asciilifeform/P4-HMD/fpga/async-fifo.v

// This file is part of the SPI controller for the Private Eye P4 HMD.
// Originally cribbed from WWW, but can't presently find where.

`default_nettype none

// Asynchronous FIFO module
module async_fifo #(

    // Parameters
    parameter DATA_SIZE = 8,  // Number of data bits
              ADDR_SIZE = 4,   // Number of bits for address
              MIN_FREE = 0 // Minimal free space for r_avail
) (

    // Inputs
    input [DATA_SIZE-1:0]      w_data,  // Data to be written to FIFO
    input                      w_en,    // Write data and increment addr.
    input                      w_clk,   // Write domain clock
    input                      w_rst,   // Write domain reset
    input                      r_en,    // Read data and increment addr.
    input                      r_clk,   // Read domain clock
    input                      r_rst,   // Read domain reset

    // Outputs
    output                     w_full,  // Flag: 1 if FIFO is full
    output reg [DATA_SIZE-1:0] r_data,  // Data to be read from FIFO
    output                     r_empty, // Flag: 1 if FIFO is empty
    output wire                avail    // 1 if FIFO has > MIN_FREE space
);

  // Constants
  localparam FIFO_DEPTH = (1 << ADDR_SIZE);

  // Internal signals
  wire [ADDR_SIZE-1:0] w_addr;
  wire [  ADDR_SIZE:0] w_gray;
  wire [ADDR_SIZE-1:0] r_addr;
  wire [  ADDR_SIZE:0] r_gray;

  // Internal storage elements
  reg  [  ADDR_SIZE:0] w_syn_r_gray;
  reg  [  ADDR_SIZE:0] w_syn_r_gray_pipe;
  reg  [  ADDR_SIZE:0] r_syn_w_gray;
  reg  [  ADDR_SIZE:0] r_syn_w_gray_pipe;

  // Declare memory
  reg  [DATA_SIZE-1:0] mem               [0:FIFO_DEPTH-1];

  //--------------------------------------------------------------------------
  // Dual-port memory (should be inferred as block RAM)

  // Write data logic for dual-port memory (separate write clock)
  // Do not write if FIFO is full!
  always @(posedge w_clk) begin
    if (w_en & ~w_full) begin
      mem[w_addr] <= w_data;
    end
  end

  // Read data logic for dual-port memory (separate read clock)
  // Do not read if FIFO is empty!
  always @(posedge r_clk) begin
    if (r_en & ~r_empty) begin
      r_data <= mem[r_addr];
    end
  end

  //--------------------------------------------------------------------------
  // Synchronizer logic

  // Pass read-domain Gray code pointer to write domain
  always @(posedge w_clk or posedge w_rst) begin
    if (w_rst == 1'b1) begin
      w_syn_r_gray_pipe <= 0;
      w_syn_r_gray <= 0;
    end else begin
      w_syn_r_gray_pipe <= r_gray;
      w_syn_r_gray <= w_syn_r_gray_pipe;
    end
  end

  // Pass write-domain Gray code pointer to read domain
  always @(posedge r_clk or posedge r_rst) begin
    if (r_rst == 1'b1) begin
      r_syn_w_gray_pipe <= 0;
      r_syn_w_gray <= 0;
    end else begin
      r_syn_w_gray_pipe <= w_gray;
      r_syn_w_gray <= r_syn_w_gray_pipe;
    end
  end

  //--------------------------------------------------------------------------
  // Instantiate incrementer and full/empty checker modules

  // Write address increment and full check module
  w_ptr_full #(
      .ADDR_SIZE(ADDR_SIZE)
  ) w_ptr_full (
      .w_syn_r_gray(w_syn_r_gray),
      .w_inc(w_en),
      .w_clk(w_clk),
      .w_rst(w_rst),
      .w_addr(w_addr),
      .w_gray(w_gray),
      .w_full(w_full)
  );

  // Read address increment and empty check module
  r_ptr_empty #(
      .ADDR_SIZE(ADDR_SIZE),
      .MIN_FREE(MIN_FREE)
  ) r_ptr_empty (
      .r_syn_w_gray(r_syn_w_gray),
      .r_inc(r_en),
      .r_clk(r_clk),
      .r_rst(r_rst),
      .r_addr(r_addr),
      .r_gray(r_gray),
      .r_empty(r_empty),
      .r_avail(avail)
  );

endmodule
